LeweeLewee/NDX2-Controller/docs/hardware/design.md

# Hardware design

Revision 0.2 — 20 September 2026. Proposal; not a wiring-ready schematic.

**D017 update, 21 September 2026:** Waveshare is selected and Android ruled out. The design below is active, but remains unvalidated electrically and mechanically. Selection does not authorize purchase.

## Preferred display assembly — HW-001

| Property | Record |
| --- | --- |
| Manufacturer / exact model | Waveshare ESP32-S3-Touch-LCD-4.3B |
| Variant | Standard, without case; SKU 27848 |
| Selection | Selected by user (D017); physical validation pending |
| Display | 4.3-inch IPS LCD, 800 x 480, capacitive touch |
| Computing | Integrated ESP32-S3, 16 MB flash, 8 MB PSRAM; no separate MCU or Wi-Fi board required |
| Mechanical reference | Manufacturer lens outline 112.4 x 75.1 mm; drawing maximum depth 17.4 +/-0.3 mm; VA 95.54 x 54.36 mm. Plugged connectors, mounting and cable bends still to verify; see River Stone study |
| Cost reference | USD 36.99 without case, checked 20 September 2026; excludes shipping and tax |
| Supply | Documented USB-C 5 V input, 7–36 V DC input and separate 3.7 V single-cell lithium battery connection |
| Battery connector | MX1.25; confirm pin count, polarity and actual board revision before specifying the harness |
| Consumption reference | Manufacturer lists 5 V / 450 mA; not our measured workload or a standby figure |
| Firmware | ESP-IDF / Arduino and LVGL examples; our Naim firmware has not been demonstrated |

Sources: [product and price](https://www.waveshare.com/product/arduino/boards-kits/esp32-s3/esp32-s3-touch-lcd-4.3b.htm), [hardware documentation](https://docs.waveshare.com/ESP32-S3-Touch-LCD-4.3B), [legacy wiki and schematic links](https://www.waveshare.com/wiki/ESP32-S3-Touch-LCD-4.3B). Manufacturer specifications are reference evidence, not bench validation. Do not substitute the 4, 4B, plain 4.3 or P4 models without review.

## Functional architecture

```mermaid
flowchart LR
    USB[Rear charging inlet - proposal] --> POWER[Charging and power path - route TBD]
    BAT[Protected large battery in base] <--> POWER
    POWER --> DISPLAY[Waveshare display and ESP32-S3]
    DISPLAY -->|Wi-Fi commands and metadata| NDX[Naim NDX 2]
    DISPLAY -. optional metadata support .-> PI[Existing Home Assistant Pi]
    PI -. native commands .-> NDX
```

The power block can be onboard or external; it does not imply a separate charger purchase. Naim and Pi power remain outside the stationary controller battery system.

## Power routes to evaluate

| Route | Advantages | Open checks |
| --- | --- | --- |
| A: protected 1S pack to documented Waveshare battery input, charging through board | Fewest extra boards; uses integrated power system | Exact schematic/revision, pack chemistry/voltage, polarity, charge current, load sharing, low-voltage shutdown, whole-board sleep |
| B: protected 1S pack with separate charger/power path and regulated 5 V into board USB-C supply | Allows independent power sizing and charge-rate choice | Converter idle current, peak current, true shutdown, USB power routing, touch wake and extra volume/cost |
| C: regulated USB battery pack for bench comparison | Quick removable power source | Low-load auto-off, restart behaviour, pass-through charging and sleep consumption; not selected for final build |

Route B is now the leading research proposal: Waveshare recommends a single cell of no more than 2,000 mAh on its battery connector, outside our initial 5–10 Ah range. Route A is on hold for the large base pack pending manufacturer clarification. This is a documented recommendation, not proof of a hard electrical capacity limit. See [power review](power-review.md).

For B, leave the onboard battery connector empty and verify the 5 V supply and programming-USB paths before wiring. Never connect a 1S pack to the 7–36 V DC input. Do not connect two chargers to the same pack. The external converter must remain enabled during touch-wake standby; full shutdown would remove touch power.

## Physical arrangement

Proposed upper assembly: display supported by its board/mounting structure, with recessed perimeter protection; no clamping load on active glass.
Proposed lower assembly: removable protected battery cradle, accessible power electronics and strain-relieved wiring.
Current physical anchor: original 01 River Stone, stationary on the table; softly rounded mineral form and non-slip feet. See [dimensioned layout](river-stone/README.md). One main shell, underside cover and one battery; no removable handheld or charge-transfer dock.
Keep Wi-Fi antenna clearance away from battery, wiring and any added ballast; follow the module's antenna guidance at CAD stage.
Use a removable underside and reusable fasteners. Exact wall thickness, tilt, screw sizes and insert lengths follow component measurements.
Use the display's existing touch cover initially; an additional overlay is optional and requires optical/touch testing.
Add separate ballast only after the battery/build mass and stability are measured.
No speaker, DAC, audio amplifier or local audio transport is required.

## Expected operating states

- Active: screen lit, Wi-Fi connected, catalogue browsing and commands.
- Connected idle: optional short interval before sleep; consumes more than deep sleep.
- Standby: backlight off, lowest viable electronics state with validated touch wake. Reconnect and retrieve fresh Naim state after wake.
- Storage off: physical disconnect/service mode; touch wake need not operate in this state.

Idle screen timeout, wake latency target, daily interaction time, desired listening-time display behaviour and recharge interval remain user-profile decisions. See [research](research.md) and [validation](validation.md).
