LeweeLewee/NDX2-Controller/docs/hardware/river-stone/fallback-waveshare.md

# Parked fallback: Waveshare River Stone

25 September 2026. User instruction D030 parks this route in favour of iPhone 11 plus the selected UGREEN Nexode 20000mAh PD 20W QC Power Bank. Preserve this work; do not continue its CAD, slicing, firmware or procurement merely from an older next-step instruction.

Last published mechanical/slicing checkpoint: **fbf917c**. The active physical proposal is [iPhone mounting](iphone-mount/README.md).

- [Packaging layout](README.md): historical plan-view allowances.
- [Shell v1](shell-v1/README.md): initial shell/cover and insertion sweep.
- [Shell v2](shell-v2/README.md): retainers and coupons.
- [Shell v3](shell-v3/README.md): strengthened rim/crown/bosses and bevel.
- [P1S slicing study](slice-v1/README.md): coupon 3MF, actual toolpath checks and two orientation estimates.

Retain all generators, STEP/STL files, reports and earlier evidence unchanged as fallback engineering. Seven v3 meshes and conservative Waveshare clearance checks passed; offline P1S slicing succeeded with recorded limitations/warning. No printed fit, glass loading, full housing, power or thermal validation was established. These results do not transfer to the iPhone or UGREEN assembly. Previously recorded purchases remain historical inventory; parking this route is not an instruction to cancel or discard them.

Resume only on an explicit return to the Waveshare route, then recheck current hardware, repo decisions and fit requirements. The old print-coupon next step is suspended.
