LeweeLewee/NDX2-Controller/docs/continuation-prompt.md

# Continuation prompt — Still Water Brief A/A.1 complete; screen selection open

> **Current override — 25 September 2026, D030:** iPhone 11 and the selected UGREEN Nexode 20000mAh PD 20W QC Power Bank are the active hardware. Waveshare CAD/slicing is parked fallback. Resume physical mounting/interface discussion from [the proposal](hardware/river-stone/iphone-mount/README.md); dimensions remain provisional. Original **01 River Stone** alone governs both body and screen/stone interface; do not use the superseded Tide pool image. Phone mounting must not obstruct microphone acoustic paths. The following Brief A closeout is historical. Do not execute Brief B or implement an iOS UI solely because screen selection is now closed.

Continue NDX2 Controller in `local/river-stone-repo`. First read `AGENTS.md`, `docs/chat-closeout-2026-09-23.md`, this prompt, `README.md`, `docs/decisions.md` (D028 and D029), and `docs/roadmap.md`. Inspect Git status/history before editing and preserve newer work, untracked materials and ignored artifacts. Working prototype b36098d and frozen `software-feasibility-v1` remain intact; do not reset/clean or replace the checkout.

The user authorized revised Still Water **Brief A and its A.1 follow-up only**, now implemented in the bridge. `docs/still-water/` is authorized revised-direction material and was preserved unchanged and is included in the same Brief A/A.1 commit. Read its README, spec sections 6/8, iphone-architecture sections 1/4/5 and evaluation. Screen selection remains open. Package statements selecting iPhone and its duplicate D028 decision draft are not adopted. D028 already records the design pause; D029 records the bridge slice. Use the next available ID for any future authorized decision. Do not implement either UI or modify firmware without a further brief.

Implemented: optional artwork `side` 1–320 and `pixel_offset` chunks through the existing authenticated action, unchanged default 80 × 80 response, bounded four-entry cache and source/registration/expiry rules; one volatile `battery_report` with integer level, charging boolean and client label; read-only `charge?` using the fresh report (below 35 yes, at least 75 no, middle follows charging; no at age >= one hour or restart). Brief A.1 adds `reason`: `window` for every fresh report, including yes; `stale` for an expired report; `none` for no report since boot. This is a D029 amendment, not a new decision. Read `docs/controller-contract-v1.md` for exact fields, chunk identity/assembly/expiry requirements and resource limits. No UI consumer or power hardware is implemented. Fixtures require no provider network or NDX.

Fresh validation for Brief A/A.1: `python -m unittest discover -s tests -v` passed 137 tests; `node --test tests/test_navigation.cjs` passed five tests; `python tools/m2_demo.py` passed six silent TLS stages including artwork, battery reporting and all three charge reasons. Windows protected temporary vault/TLS tests required normal host execution outside the restricted sandbox; no ACL/trust checks were weakened. No fresh firmware/native build, live playback/volume or physical validation is claimed. Review evidence and rerun appropriate tests after subsequent changes.

Preserve authenticated TLS, provisioned trust, protected persistence, durable command suppression, unknown outcomes, no replay/automatic re-pairing, D011 and native Naim TIDAL. No new unauthenticated or credential-free route of any kind. On-table prototype trials use a private artifact link or throwaway static server outside the repository, never the bridge. The existing envelope has bounded single-worker concurrency, socket/request/response limits and provider limits, but no standalone requests-per-second limiter; do not claim one.

Keep the functional prototype, transport fixes, preferences, recovery, enrollment/setup/trust and packaging infrastructure. Consult the relevant `m2-*` runbooks before changes. Physical screen/touch/wake/microphone/power gates, HP-01 applicability after screen selection and Pi suitability remain open. No live audible tests, flashing, efuse changes, physical provisioning or Pi installation under this scope. Keep private information and generated artifacts in ignored `local/`. Update evidence, decisions and roadmap only for supported claims and authorized choices. Prior continuation `m2-continuation-before-revised-direction.md` is history, not authorization to resume visual work.
