LeweeLewee/NDX2-Controller/docs/still-water/codex-prompt-A.md

First read `AGENTS.md`, `docs/chat-closeout-2026-09-23.md` and `docs/continuation-prompt.md`. This task authorises Brief A under the revised Still Water direction. Preserve the working prototype and newer work. Screen selection remains open; do not implement either UI yet. D028 already records the design pause; use the next available decision ID for new decisions.

Continue NDX2 Controller in `local/river-stone-repo`. Read `docs/still-water/README.md`, `docs/still-water/spec.md` sections 6 and 8, `docs/still-water/iphone-architecture.md` sections 1, 4 and 5, and `docs/still-water/evaluation.md`. Do not change `firmware/` or any UI in this task. Do not record the iPhone decision; the screen selection is open and D028 already records the design pause. `docs/still-water/` is authorised revised-direction material under this task; preserve it and the working prototype at b36098d.

Add to the bridge, with tests, all as read paths or bounded writes under the existing authenticated envelope and rate limits: (1) an artwork preview size up to 320 × 320 alongside the existing 80 × 80 path, same normalisation, registration and expiry rules, within the existing memory and response bounds (this is authorised by the revised direction; it is not the automatic resolution increase the closeout paused); (2) a battery report action from a display client carrying level, charging state and a client id, stored as the last report only; (3) a `charge?` query for a stone power module returning yes or no from the last battery report with a 35% to 75% window and "no" when there is no report younger than one hour. No new unauthenticated or credential-free route of any kind: the on-table prototype trial uses the private artifact link or a throwaway static server outside the repository, not the bridge. Keep the fixture bridge able to drive all of this without a network or an NDX.

Validation: `python -m unittest discover -s tests -v`, `node --test tests/test_navigation.cjs`, `python tools/m2_demo.py`. Update `docs/roadmap.md` and `docs/continuation-prompt.md`. No live playback, volume or NDX mutations.
