LeweeLewee/NDX2-Controller/docs/m2-visual-polish.md

# Native visual polish - 23 September 2026

The user confirmed the repaired transport controls and requested a very high-end finish for the coffee-table controller. This pass refines the approved D020 layout in shared LVGL; the hash-identified browser design is unchanged.

## Implemented

- A consistent native outline icon family for transport, amplifier, search, microphone, navigation, Settings and list membership. Paths follow the approved 24-unit design language; no font/image download or bitmap icon dependency. Disabled opacity and generous existing hit areas remain.
- Paper-colour track text, larger artist text, quieter album/source metadata, matching timeline colours and clearer type hierarchy. Existing Montserrat fonts remain; this is not a claim of exact Segoe UI font parity.
- Quiet right-aligned connection status with explicit Silent demo labelling. Pending, stale/offline, errors and unknown outcomes remain visible. Battery unavailability stays in Device rather than occupying every screen. Normal in-flight reads do not falsely label a fresh connection stale.
- Separated bottom navigation with outlined icons, selected surface and fine accent underline. Palette roles apply consistently to sage, sand and slate surfaces, dividers and secondary text.
- List separators and artist/type subtitles; read-only queue titles stay legible. Structured two-line Settings rows, themed slider/dropdown/keyboard, primary Play emphasis and rounded artwork clipping. Missing artwork has a quiet disc mark and explicit unavailable caption, not a fabricated cover.
- Decorative children do not consume taps. The preferences smoke locates controls by LVGL class rather than incidental decorative child order.

## Fresh validation

- Desktop build and all five CTests passed.
- Native SDL/LVGL with authenticated silent TLS fixture passed the full screen/Back/play/voice/follow/library/settings/wake sequence and artwork pixel checks. One run timed out at stage 21 waiting for library state; an unchanged rerun passed. This intermittent harness/interaction timing result is retained, not presented as an unqualified repeated pass or attributed to a proven cause.
- Standalone and TLS transport pointer/pixel checks passed: pause/resume, next/previous and wrapping, one request per tap.
- Separate-process preference persistence and restored palette pixels passed.
- Recovery fault injection passed startup outage, delayed read, lost mutation responses and bridge restart, with one silent play and one simulated amplifier call and no replay.
- Actual 800 x 480 captures inspected for Playing, Find/long row, detail/long title, Settings, Display, and standalone sage/slate. All three palette fixtures completed the transport sequence. Captures and logs remain under ignored `local/m2/`.
- ESP32 build passed: `0x98210` bytes, 41% application partition free. No flashing or physical performance claim.
- Approved HTML SHA-256 remains `1886dfe3f6bea33d8206bbe27b0c799a45964c995144131ef02a9619a3c68bbc`; frozen feasibility tag remains `aa070fc0af4a616f769a7c0f15790831c90c112c`.

## Remaining quality gates

This is a native visual-polish checkpoint, not final user or physical acceptance. Artwork is still an 80 x 80 authenticated preview stretched to the approved cover space; improving photographic resolution and checking bounded memory/transport cost is the next major visual-quality slice. Real metadata/artwork need the NDX network. Physical contrast, seated readability, touch, frame timing and power remain HP-01/P3/P4/P5 work. The intermittent full-smoke library wait should be investigated if it recurs; do not add mutation retries to mask it.

Playback, native Naim resolution, D011, authentication, protected state and recovery logic are unchanged. No live audio, hardware provisioning, flashing or Pi deployment occurred. Python/backend and JavaScript suites were not rerun for this presentation-only slice; earlier results remain historical.
