LeweeLewee/NDX2-Controller/docs/still-water/reference/01-sleep.png

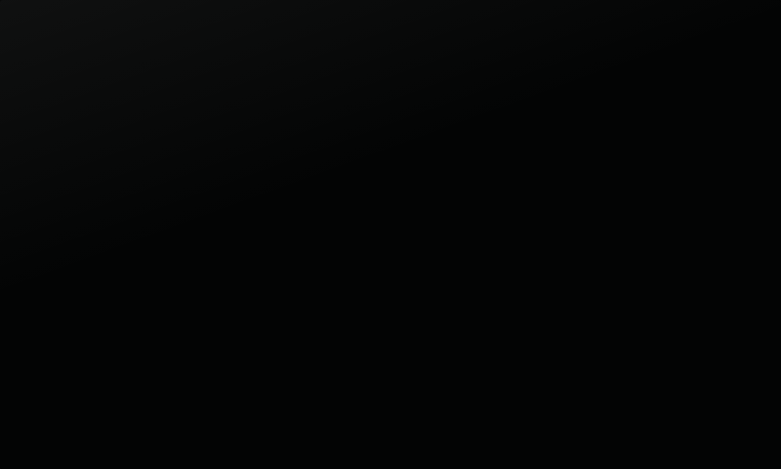
docs/still-water/reference/01-sleep.png
