LeweeLewee/NDX2-Controller/docs/still-water/reference/02-presence.png

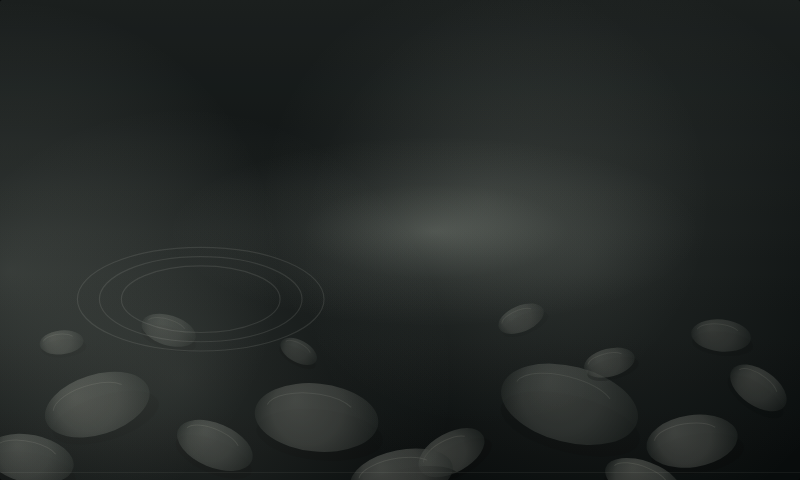
docs/still-water/reference/02-presence.png
