LeweeLewee/NDX2-Controller/docs/still-water/reference/04-wake.png

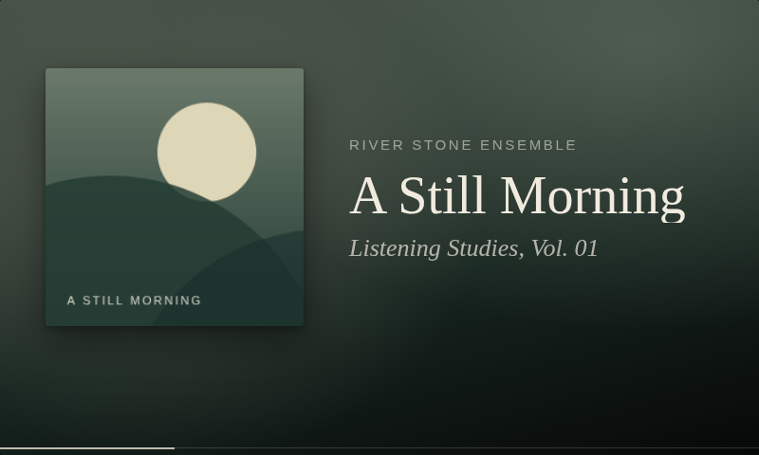
docs/still-water/reference/04-wake.png
