LeweeLewee/NDX2-Controller/docs/still-water/reference/06-touched.png

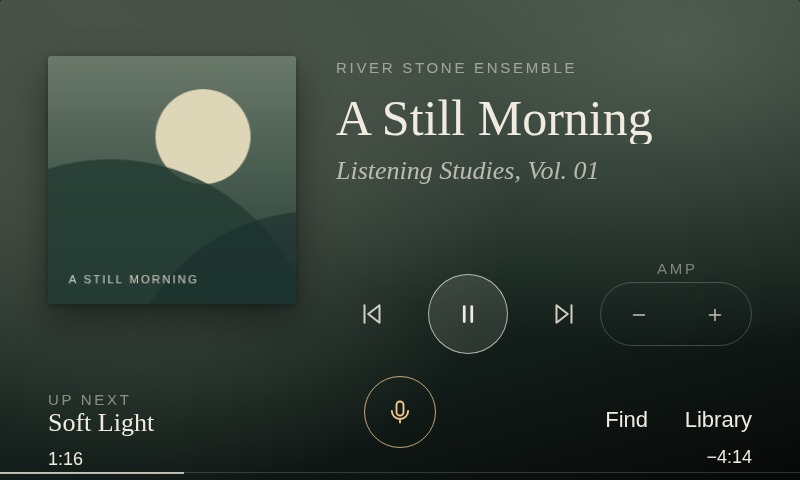
docs/still-water/reference/06-touched.png
