LeweeLewee/NDX2-Controller/docs/still-water/reference/07-river.png

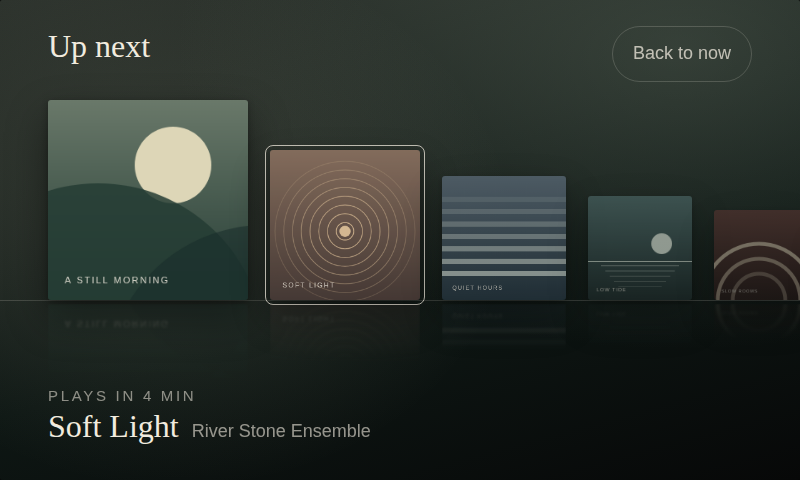
docs/still-water/reference/07-river.png
