LeweeLewee/NDX2-Controller/docs/still-water/reference/08-ask.png

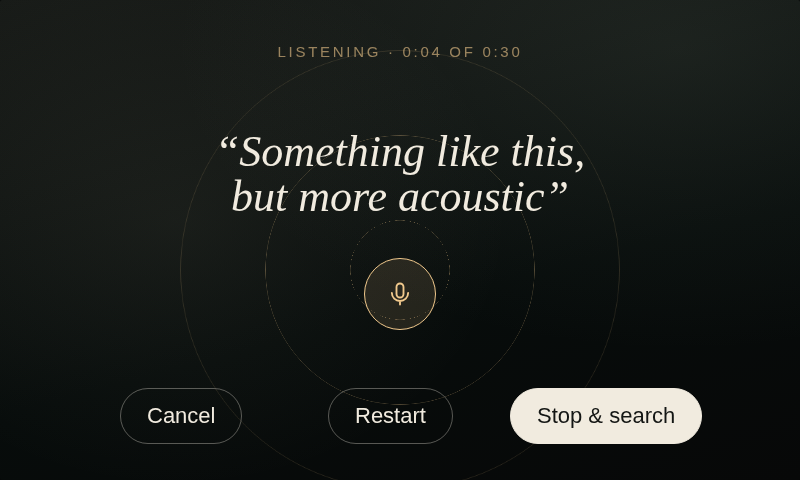
docs/still-water/reference/08-ask.png
