LeweeLewee/NDX2-Controller/docs/still-water/reference/09-three.png

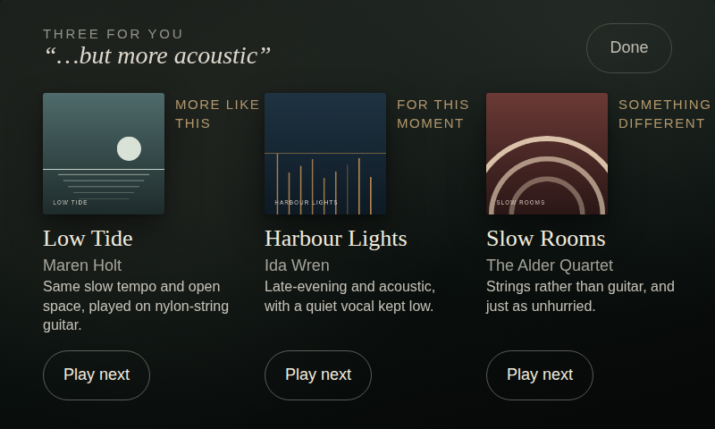
docs/still-water/reference/09-three.png
