LeweeLewee/NDX2-Controller/docs/still-water/reference/11-stopped.png

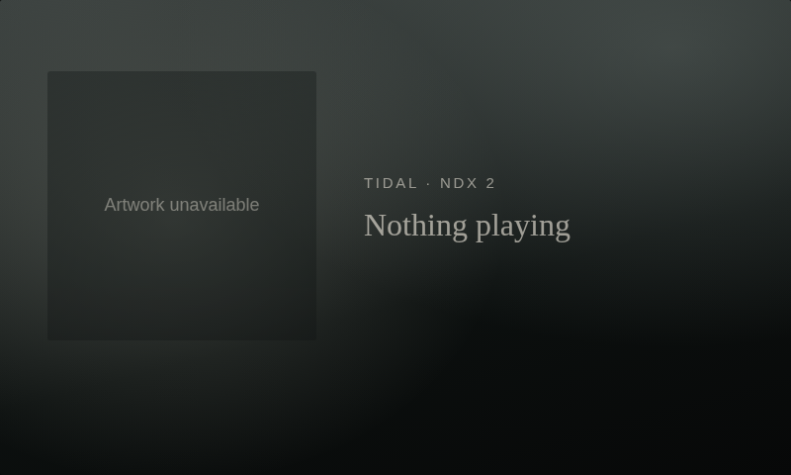
docs/still-water/reference/11-stopped.png
