LeweeLewee/NDX2-Controller/docs/still-water/reference/18-keyboard.png

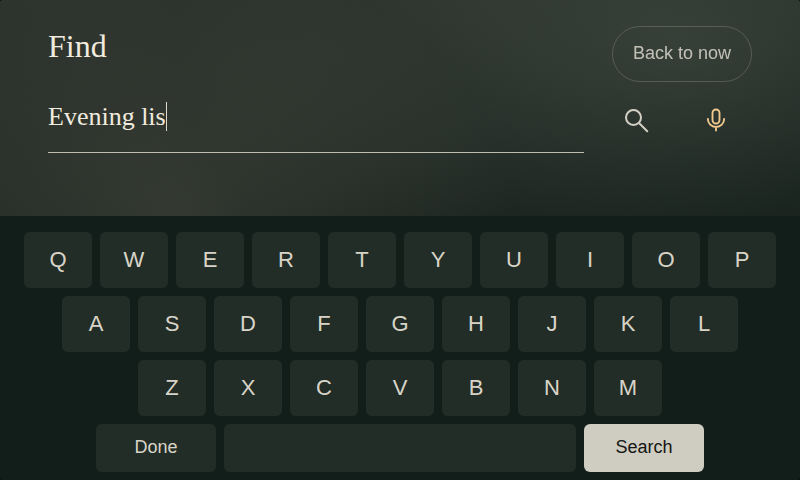
docs/still-water/reference/18-keyboard.png
