LeweeLewee/NDX2-Controller/docs/still-water/reference/19-detail.png

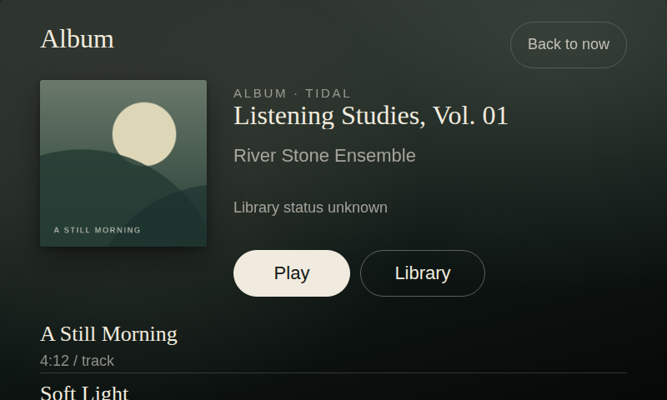
docs/still-water/reference/19-detail.png
