LeweeLewee/NDX2-Controller/docs/still-water/reference/20-library.png

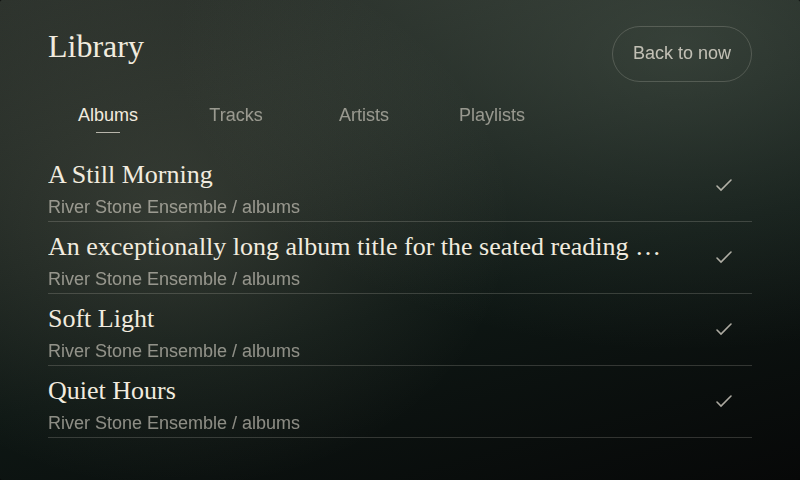
docs/still-water/reference/20-library.png
