LeweeLewee/NDX2-Controller/docs/still-water/reference/22-display.png

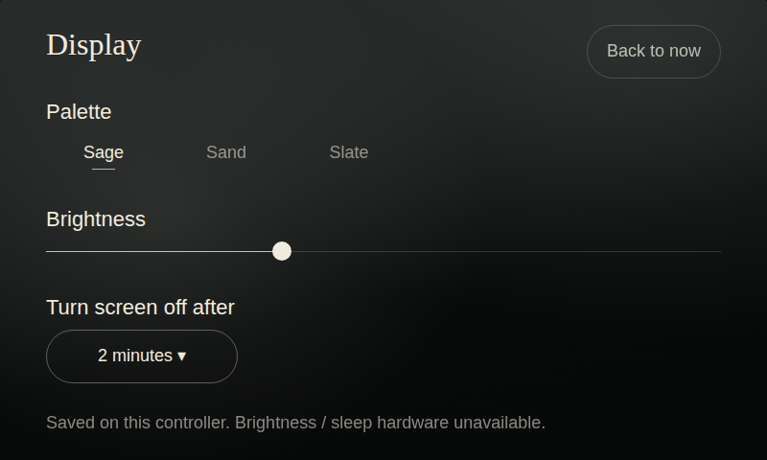
docs/still-water/reference/22-display.png
